roboime/HRR/Firmware/F407-HRR-Firmware/Core/Src/Components/Motor.hpp

/*
 * Motor.hpp
 *
 *  Created on: May 21, 2023
 *      Author: Gabriel
 */

#ifndef SRC_COMPONENTS_MOTOR_HPP_
#define SRC_COMPONENTS_MOTOR_HPP_

class Motor {
public:
	Motor();
	virtual ~Motor();
};

#endif /* SRC_COMPONENTS_MOTOR_HPP_ */
