roboime/HRR/Firmware/F407-HRR-Firmware/Core/Src/Components/PWMServo.hpp

/*
 * PWMServo.hpp
 *
 *  Created on: May 16, 2022
 *      Author: Gabriel
 */

#ifndef SRC_COMPONENTS_PWMSERVO_HPP_
#define SRC_COMPONENTS_PWMSERVO_HPP_

#include "main.h"

class PWMServo {
public:
	PWMServo();
};

#endif /* SRC_COMPONENTS_PWMSERVO_HPP_ */
