roboime/HRR/Firmware/F407-HRR-Firmware/Core/Src/Components/Start.cpp

/*
 * Start.cpp
 *
 *  Created on: May 16, 2022
 *      Author: Gabriel
 */

#include "Start.hpp"
#include "Robot.hpp"

#include <cstring>

extern TIM_HandleTypeDef htim6;
extern UART_HandleTypeDef huart4;

Robot robot;

void HAL_TIM_PeriodElapsedCallback(TIM_HandleTypeDef *htim){
	if(htim==&htim6){
		HAL_GPIO_WritePin(GPIOE,  GPIO_PIN_2, GPIO_PIN_SET);
		uint8_t receivedByte;
		if(HAL_UART_Receive(&huart4, &receivedByte, 1, 0) == HAL_OK){	//Verifica se recebeu byte na porta serial
			robot.setMovement((Robot::stepTypeDef)(receivedByte - 48));	//Combinado com a intel de receber em ASCII
		}
		if (robot.status == Robot::STATUS_READY){
			robot.controlCallback();	//Controle
		}
		HAL_GPIO_WritePin(GPIOE,  GPIO_PIN_2, GPIO_PIN_RESET);
	}
}

void Start(){
	robot.init();
	uint32_t a = TIM6->ARR;
	//para setar os zeros dos motores se baseiem no risco no disco do motor do datasheet dele e este risco será a metade da posiçao ou seja 512 ou 2048
	//para saber se os zeros dos motores funcionaram comente a linha abaixo:
	robot.setMovement(Robot::STEP_FORWARD); // (primeiro comando antes de a intel comunicar(no ex é step forward)) Força o robô a andar, mas não vai ser necessário com o uso da Raspberry Pi
	while (true){
		//Não faz nada (tudo na interrupção e na máquina de estados)
	}
}
