roboime/HRR/Firmware/F407-HRR-Firmware/Core/Src/Components/Start.hpp

/*
 * Start.hpp
 *
 *  Created on: May 16, 2022
 *      Author: Gabriel
 */

#ifndef SRC_COMPONENTS_START_HPP_
#define SRC_COMPONENTS_START_HPP_

#include "main.h"

#ifdef __cplusplus
extern "C" {
#endif

void Start();

#ifdef __cplusplus
}
#endif

#endif /* SRC_COMPONENTS_START_HPP_ */
