roboime/HRR/Firmware/ID_Set_and_Test/Core/Src/main.c

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
/* Includes ------------------------------------------------------------------*/
#include "main.h"
#include "usb_device.h"

 ADC_HandleTypeDef hadc1;
DMA_HandleTypeDef hdma_adc1;

SD_HandleTypeDef hsd;

SPI_HandleTypeDef hspi1;
SPI_HandleTypeDef hspi2;

TIM_HandleTypeDef htim3;
TIM_HandleTypeDef htim4;

UART_HandleTypeDef huart4;
UART_HandleTypeDef huart1;
UART_HandleTypeDef huart2;
UART_HandleTypeDef huart3;
UART_HandleTypeDef huart6;
DMA_HandleTypeDef hdma_usart1_tx;
DMA_HandleTypeDef hdma_usart2_tx;
DMA_HandleTypeDef hdma_usart3_tx;
DMA_HandleTypeDef hdma_usart6_tx;

void SystemClock_Config(void);
static void MX_GPIO_Init(void);
static void MX_SPI1_Init(void);
static void MX_SDIO_SD_Init(void);
static void MX_DMA_Init(void);
static void MX_SPI2_Init(void);
static void MX_TIM3_Init(void);
static void MX_TIM4_Init(void);
static void MX_USART1_UART_Init(void);
static void MX_USART2_UART_Init(void);
static void MX_USART3_UART_Init(void);
static void MX_USART6_UART_Init(void);
static void MX_ADC1_Init(void);
static void MX_UART4_Init(void);
/* USER CODE BEGIN 0 */
	uint8_t uartBuf[64];
	uint8_t paramArray[2];  // contem os parametros de setar id
	uint8_t paramArray2[5];  // parametros da primeira posiçao
	uint8_t paramArray3[5];  // parametros da segunda posiçao
	uint8_t motorId = 0xFE;  // ID de broadcast
	uint8_t novoId = 0x00;	 //novo ID (se mudar tem q mudar o uartbuf2 do sendInstruction)
	uint8_t paramArray[2];  // array com os parametros de set id
	uint16_t pos1 = 1000;
	uint16_t pos2 = 500;
	uint16_t spd = 500;


  void sendInstruction(uint8_t instruction, uint8_t* paramArray, uint8_t numParams){
	  //while(huartptr->gState != HAL_UART_STATE_READY);	//Tem que implementar timeout
	  uartBuf[0] = 0xFF;				//Header
	  uartBuf[1] = 0xFF;				//Header
	  uartBuf[2] = motorId;				//ID
	  uartBuf[3] = numParams + 2;		//Length
	  uartBuf[4] = instruction;			//Instruction
	  uint8_t i;
	  uint8_t somaParams = 0;
	  for(i=0; i<numParams; i++){
		  uartBuf[i+5] = paramArray[i];	//Parameters
		  somaParams += paramArray[i];
	  }
	  uartBuf[i+5] = ~(motorId + numParams + 2 + instruction + somaParams);	//Checksum
	  HAL_UART_Transmit(&huart1, (uint8_t *)uartBuf, numParams + 6, 100);  //tem q ficar mudando a porta aqui
}

/* USER CODE END 0 */

/**
  * @brief  The application entry point.
  * @retval int
  */
int main(void)
{
  /* MCU Configuration--------------------------------------------------------*/

  /* Reset of all peripherals, Initializes the Flash interface and the Systick. */
  HAL_Init();

  /* USER CODE BEGIN Init */
  HAL_HalfDuplex_EnableTransmitter(&huart1);  // ativa o modo transmissor

  paramArray[0] = 0x03; 		//Starting adress da instruçao de ID
  paramArray[1] = novoId; 	//novo ID (se mudar tem q mudar o uartbuf2 do sendInstruction)

  paramArray2[0] = 30;			//Goal position
  paramArray2[1] = pos1;			//Conferir endianess
  paramArray2[2] = pos1>>8;
  paramArray2[3] = spd;
  paramArray2[4] = spd>>8;

  paramArray3[0] = 30;			//Goal position
  paramArray3[1] = pos2;		//Conferir endianess
  paramArray3[2] = pos2>>8;
  paramArray3[3] = spd;
  paramArray3[4] = spd>>8;
  while(1){
  sendInstruction(0x03, paramArray2, 5);
  	  HAL_Delay(2000);
  	  sendInstruction(0x03, paramArray3, 5);
  	  HAL_Delay(2000);
  }
  /* USER CODE END Init */

  /* Configure the system clock */
  SystemClock_Config();

  /* Initialize all configured peripherals */
  MX_GPIO_Init();
  MX_SPI1_Init();
  MX_USB_DEVICE_Init();
  MX_SDIO_SD_Init();
  MX_DMA_Init();
  MX_SPI2_Init();
  MX_TIM3_Init();
  MX_TIM4_Init();
  MX_USART1_UART_Init();
  MX_USART2_UART_Init();
  MX_USART3_UART_Init();
  MX_USART6_UART_Init();
  MX_ADC1_Init();
  MX_UART4_Init();
  /* USER CODE BEGIN 2 */
  sendInstruction(0x03, paramArray, 2);  // set ID
  /* USER CODE END 2 */

  /* Infinite loop */
  /* USER CODE BEGIN WHILE */
  while (1)
  {



    /* USER CODE END WHILE */

    /* USER CODE BEGIN 3 */
  }
  /* USER CODE END 3 */
}

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
